JosepVirgili/WedBooth/CAD/2DCAD/Bottom.dxf

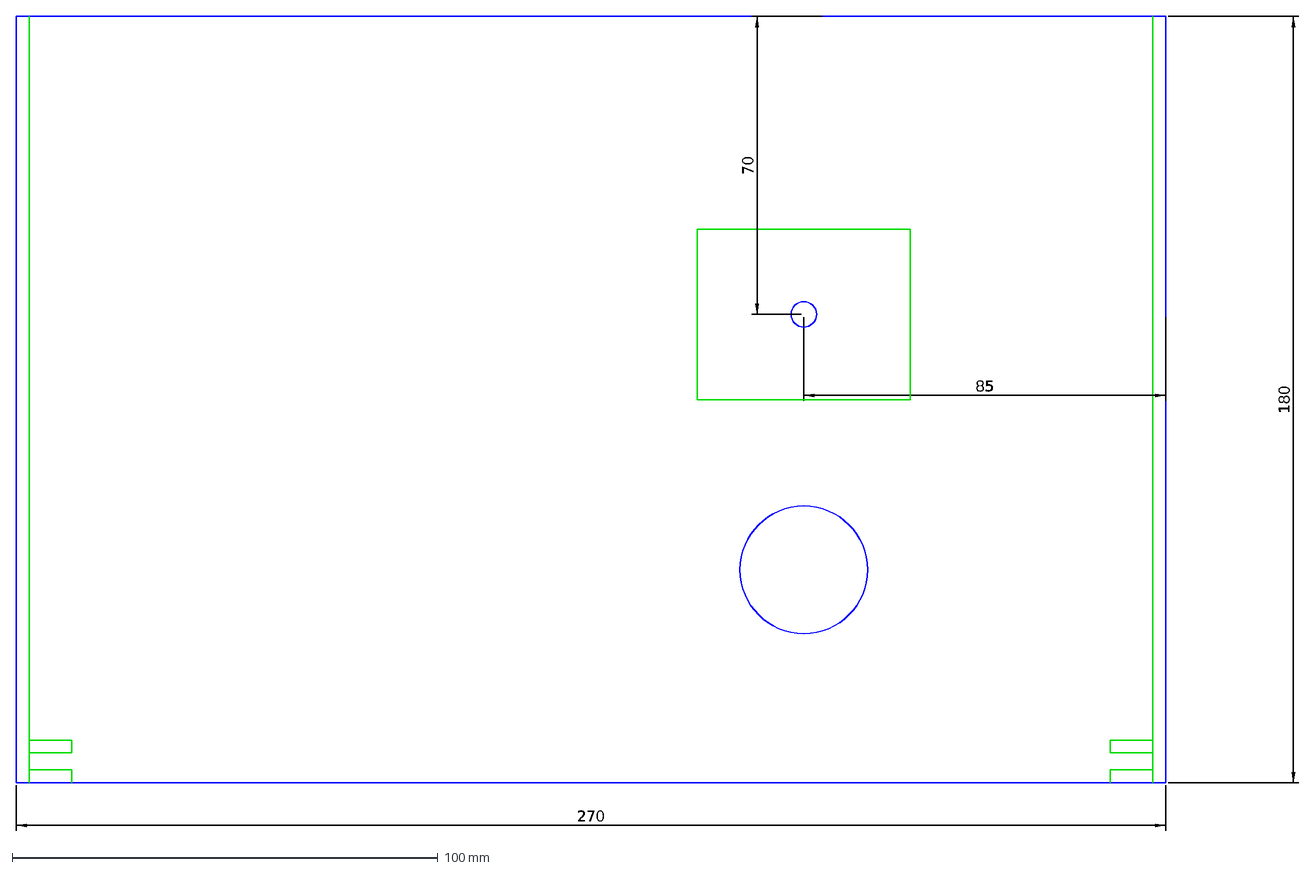
[picture p19: CAD file, 2014-10-03]
CAD/2DCAD/Bottom.dxf
270
180
85
70
