JosepVirgili/WedBooth/CAD/2DCAD/NoComments/Block_Front_x4_NoCom.dxf

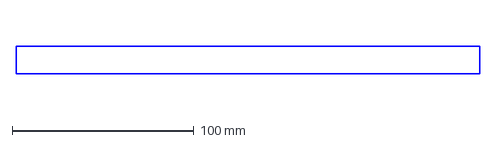
[picture p20: CAD file, 2014-10-03]
CAD/2DCAD/NoComments/Block_Front_x4_NoCom.dxf
255.0 x 15.0 mm
